netmb/hap/firmware/2.5.13/hars.c

////////////////////////////////////////////////////////////////////////////////
// Projekt:              Home-Automation                                      //
// Modul:                Rollladensteuerung                                   //
// Version:              1.0 (2)                                              //
////////////////////////////////////////////////////////////////////////////////
// Erstellt am:          11.01.2007                                           //
// Erstellt von:         Holger Heuser                                        //
// Zuletzt geändert am:  05.10.2011                                           //
// Zuletzt geändert von: Carsten Wolff                                        //
////////////////////////////////////////////////////////////////////////////////


////////////////////////////////////////////////////////////////////////////////
// Module einbinden                                                           //
////////////////////////////////////////////////////////////////////////////////

#include <mv.h>

#ifdef COHARS

// Basis Module ////////////////////////////////////////////////////////////////

#include <stdlib.h>

// Essentielle Module //////////////////////////////////////////////////////////

#include <hakm.h>
#include <hasm.h>

// Optionale Module ////////////////////////////////////////////////////////////

#ifdef COHABZ
#include <habz.h>
#endif

#include <haam.h>
#include <hars.h>


////////////////////////////////////////////////////////////////////////////////
// Precompiler Konstanten                                                     //
////////////////////////////////////////////////////////////////////////////////

#define RSTimerPrescale 20

#define RSStatusStill 0x00
#define RSStatusUp 0x01
#define RSStatusDown 0x02
#define RSControlFlag 0x80

#define RSMaxTimeTolUp 1.25
#define RSMaxTimeTolDown 1.2
#define RSUpKorr 1.05

#define RSTypeImpSteuer 1
#define RSImpLengthC 3


////////////////////////////////////////////////////////////////////////////////
// Typdefinitionen                                                            //
////////////////////////////////////////////////////////////////////////////////

typedef struct {
  tAMProp *CP;
  tByte Value;
  tByte ValueNew;
  tWord Counter;
  tWord Time;
  tByte Status;
  signed char ImpSteuerUpC;
  signed char ImpSteuerDownC;
} tRSStatusElement;

typedef struct {
  tByte N;
  tRSStatusElement *E;
} tRSStatus;


////////////////////////////////////////////////////////////////////////////////
// Globale Variablen                                                          //
////////////////////////////////////////////////////////////////////////////////

tRSStatus RSS;
tByte RSCounter;
tByte Control;
int tmp;


////////////////////////////////////////////////////////////////////////////////
// Funktionen                                                                 //
////////////////////////////////////////////////////////////////////////////////

void RSInit(void) {
  
  tByte i;

  RSS.N = AMMIInit(KMAMRS, KMAMRSMask);
  RSS.E = malloc(sizeof(tRSStatusElement) * RSS.N);
  for(i = 0; i < RSS.N; i++) {
    RSS.E[i].CP = AMMIGetMProp();
    RSS.E[i].Value = 0;
    RSS.E[i].ValueNew = 0;
    RSS.E[i].Counter = 0;
	RSS.E[i].Time = 0;
    RSS.E[i].Status = RSStatusStill;
    RSS.E[i].ImpSteuerUpC = -1;
    RSS.E[i].ImpSteuerDownC = -1;
  }
  RSCounter = 0;
  Control   = 0;
}

void RSSetValue(tByte pX, tByte pValue) {
  while(Control == 1) {
// Warte solange RSControl ausgeführt wird
  }
  if((RSS.E[pX].Status & 0x03) == RSStatusStill) {
    if(RSS.E[pX].Value > pValue || pValue == 0) {
      if(pValue == 0)
        RSS.E[pX].Counter = RSS.E[pX].CP->RS.MaxTime * RSMaxTimeTolUp;
      else
        RSS.E[pX].Counter = (RSS.E[pX].Value - pValue) * RSS.E[pX].CP->RS.MaxTime * RSUpKorr / 100;
      RSS.E[pX].Time = RSS.E[pX].Counter;
	  RSS.E[pX].Status = (RSS.E[pX].Status & 0xFC) | RSStatusUp;
      if((RSS.E[pX].CP->RS.Type & RSTypeImpSteuer) == RSTypeImpSteuer)
        RSS.E[pX].ImpSteuerUpC = RSImpLengthC;
	  SMSetOutput(RSS.E[pX].CP->RS.OPDown.Modul, RSS.E[pX].CP->RS.OPDown.Addr, 0, 0, 0);	
      SMSetOutput(RSS.E[pX].CP->RS.OPUp.Modul, RSS.E[pX].CP->RS.OPUp.Addr, 100, 0, 0);
    }
    if(RSS.E[pX].Value < pValue || pValue == 100) {
      if(pValue == 100)
	    RSS.E[pX].Counter = RSS.E[pX].CP->RS.MaxTime * RSMaxTimeTolDown;
	  else
        RSS.E[pX].Counter = (pValue - RSS.E[pX].Value) * RSS.E[pX].CP->RS.MaxTime / 100;
	  RSS.E[pX].Time = RSS.E[pX].Counter;
      RSS.E[pX].Status = (RSS.E[pX].Status & 0xFC) | RSStatusDown;
      if((RSS.E[pX].CP->RS.Type & RSTypeImpSteuer) == RSTypeImpSteuer)
        RSS.E[pX].ImpSteuerDownC = RSImpLengthC;
	  SMSetOutput(RSS.E[pX].CP->RS.OPUp.Modul, RSS.E[pX].CP->RS.OPUp.Addr, 0, 0, 0);	
      SMSetOutput(RSS.E[pX].CP->RS.OPDown.Modul, RSS.E[pX].CP->RS.OPDown.Addr, 100, 0, 0);
    }
    RSS.E[pX].ValueNew = pValue;
    SMSendStatus(RSS.E[pX].CP->SModul, RSS.E[pX].CP->Addr, pValue, 0);
  }
  else
    SMSendProtErr(SMPECDeviceBusy, RSS.E[pX].CP->Addr, 0, 0);
}

void RSControlInvert(tByte pX) {
  if(RSS.E[pX].Status & 0x03)
    RSControlStop(pX);
  else
    if(RSGetValue(pX) > 0)
      RSSetValue(pX, 0);
    else
      RSSetValue(pX, 100);
}

void RSControlUp(tByte pX) {
  if(RSS.E[pX].Status & 0x03)
    RSControlStop(pX);
  else
    RSSetValue(pX, 0);
}

void RSControlDown(tByte pX) {
  if(RSS.E[pX].Status & 0x03)
    RSControlStop(pX);
  else
    RSSetValue(pX, 100);
}

void RSControlStop(tByte pX) {
  while(Control == 1) {
// Warte solange RSControl ausgeführt wird
  }
  if(RSS.E[pX].ValueNew > RSS.E[pX].Value)
    tmp = RSS.E[pX].Value + ((RSS.E[pX].Time - RSS.E[pX].Counter) * 100 / RSS.E[pX].CP->RS.MaxTime);
  else 
    tmp = RSS.E[pX].Value - ((RSS.E[pX].Time - RSS.E[pX].Counter) * 100 / (RSS.E[pX].CP->RS.MaxTime * RSUpKorr)); 
  if(tmp < 0) tmp = 0;
  if(tmp > 100) tmp = 100;
  RSS.E[pX].Value = tmp;
  RSS.E[pX].Counter = 0;
  RSS.E[pX].Time = 0;
  RSS.E[pX].ValueNew = RSS.E[pX].Value;
  SMSendStatus(RSS.E[pX].CP->SModul, RSS.E[pX].CP->Addr, RSGetValue(pX), 0);
}

void RSControlStart(tByte pX) {
  if(RSS.E[pX].Status & RSControlFlag)
    RSControlDown(pX);
  else
    RSControlUp(pX);
  RSS.E[pX].Status ^= RSControlFlag;
}

inline tByte RSGetValue(tByte pX) {
  return RSS.E[pX].Value;
}

inline void RSCounterInc(void) {
  RSCounter++;
}

void RSControl(void) {

  tByte i;
 
  if(RSCounter >= RSTimerPrescale) {
    RSCounter = 0;
	Control   = 1;
    for(i = 0; i < RSS.N; i++) {
      if(RSS.E[i].ImpSteuerUpC >= 0) RSS.E[i].ImpSteuerUpC--;
      if(RSS.E[i].ImpSteuerUpC == 0)
        SMSetOutput(RSS.E[i].CP->RS.OPUp.Modul, RSS.E[i].CP->RS.OPUp.Addr, 0, 0, 0);
      if(RSS.E[i].ImpSteuerDownC >= 0) RSS.E[i].ImpSteuerDownC--;
      if(RSS.E[i].ImpSteuerDownC == 0)
        SMSetOutput(RSS.E[i].CP->RS.OPDown.Modul, RSS.E[i].CP->RS.OPDown.Addr, 0, 0, 0);
      if(RSS.E[i].Counter > 0) {
        RSS.E[i].Counter--;
      }
      else {
        if((RSS.E[i].Status & 0x03) == RSStatusUp) {
          RSS.E[i].Status = (RSS.E[i].Status & 0xFC) | RSStatusStill;
          if((RSS.E[i].CP->RS.Type & RSTypeImpSteuer) == RSTypeImpSteuer) {
            RSS.E[i].ImpSteuerUpC = RSImpLengthC;
			SMSetOutput(RSS.E[i].CP->RS.OPDown.Modul, RSS.E[i].CP->RS.OPDown.Addr, 0, 0, 0);
            SMSetOutput(RSS.E[i].CP->RS.OPUp.Modul, RSS.E[i].CP->RS.OPUp.Addr, 100, 0, 0);
          }
          else
            SMSetOutput(RSS.E[i].CP->RS.OPUp.Modul, RSS.E[i].CP->RS.OPUp.Addr, 0, 0, 0);
        }
        if((RSS.E[i].Status & 0x03) == RSStatusDown) {
          RSS.E[i].Status = (RSS.E[i].Status & 0xFC) | RSStatusStill;
          if((RSS.E[i].CP->RS.Type & RSTypeImpSteuer) == RSTypeImpSteuer) {
            RSS.E[i].ImpSteuerDownC = RSImpLengthC;
			SMSetOutput(RSS.E[i].CP->RS.OPUp.Modul, RSS.E[i].CP->RS.OPUp.Addr, 0, 0, 0);
            SMSetOutput(RSS.E[i].CP->RS.OPDown.Modul, RSS.E[i].CP->RS.OPDown.Addr, 100, 0, 0);
          }
          else
            SMSetOutput(RSS.E[i].CP->RS.OPDown.Modul, RSS.E[i].CP->RS.OPDown.Addr, 0, 0, 0);
        }
		RSS.E[i].Time = 0;
        RSS.E[i].Value = RSS.E[i].ValueNew;
      }
    }
	Control = 0;
  }
}

inline void RSDestroy(void) {
  free(RSS.E);
}

#endif
