netmb/hap/firmware/2.5.13/hagl.c

////////////////////////////////////////////////////////////////////////////////
// Projekt:              Home-Automation                                      //
// Modul:                Global                                               //
// Version:              2.1 (0)                                              //
////////////////////////////////////////////////////////////////////////////////
// Erstellt am:          20.12.2005                                           //
// Erstellt von:         Holger Heuser                                        //
// Zuletzt geändert am:  21.01.2006                                           //
// Zuletzt geändert von: Holger Heuser                                        //
////////////////////////////////////////////////////////////////////////////////


////////////////////////////////////////////////////////////////////////////////
// Module einbinden                                                           //
////////////////////////////////////////////////////////////////////////////////

#include <hagl.h>


////////////////////////////////////////////////////////////////////////////////
// Funktionen                                                                 //
////////////////////////////////////////////////////////////////////////////////

tWord BytesToWord(tByte pLByte, tByte pHByte) {

  tWord Result;
  
  Result = pHByte;
  Result = Result << 8;
  Result = Result | pLByte;
  return Result;
}
